MarcinWachowiak/analog-rf-phase-shifter-module/rf_phase_shifter_discrete_2_45GHz/qucs_sim_prj/plots/pha_l_ser_and_c_par_sweep.png

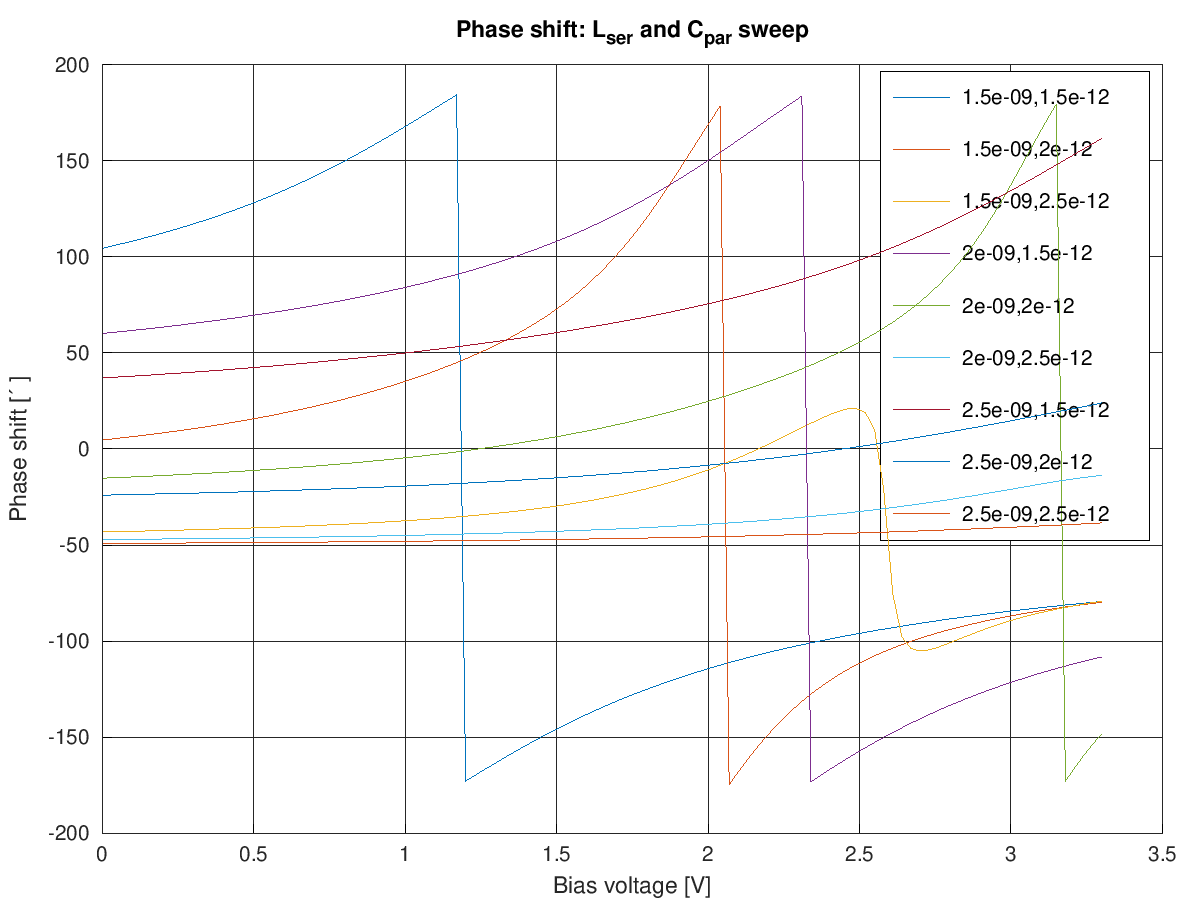
rf_phase_shifter_discrete_2_45GHz/qucs_sim_prj/plots/pha_l_ser_and_c_par_sweep.png
