MarcinWachowiak/analog-rf-phase-shifter-module/rf_phase_shifter_discrete_2_45GHz/qucs_sim_prj/plots/ripp_and_max_phase_shift_l_ser_sweep.png

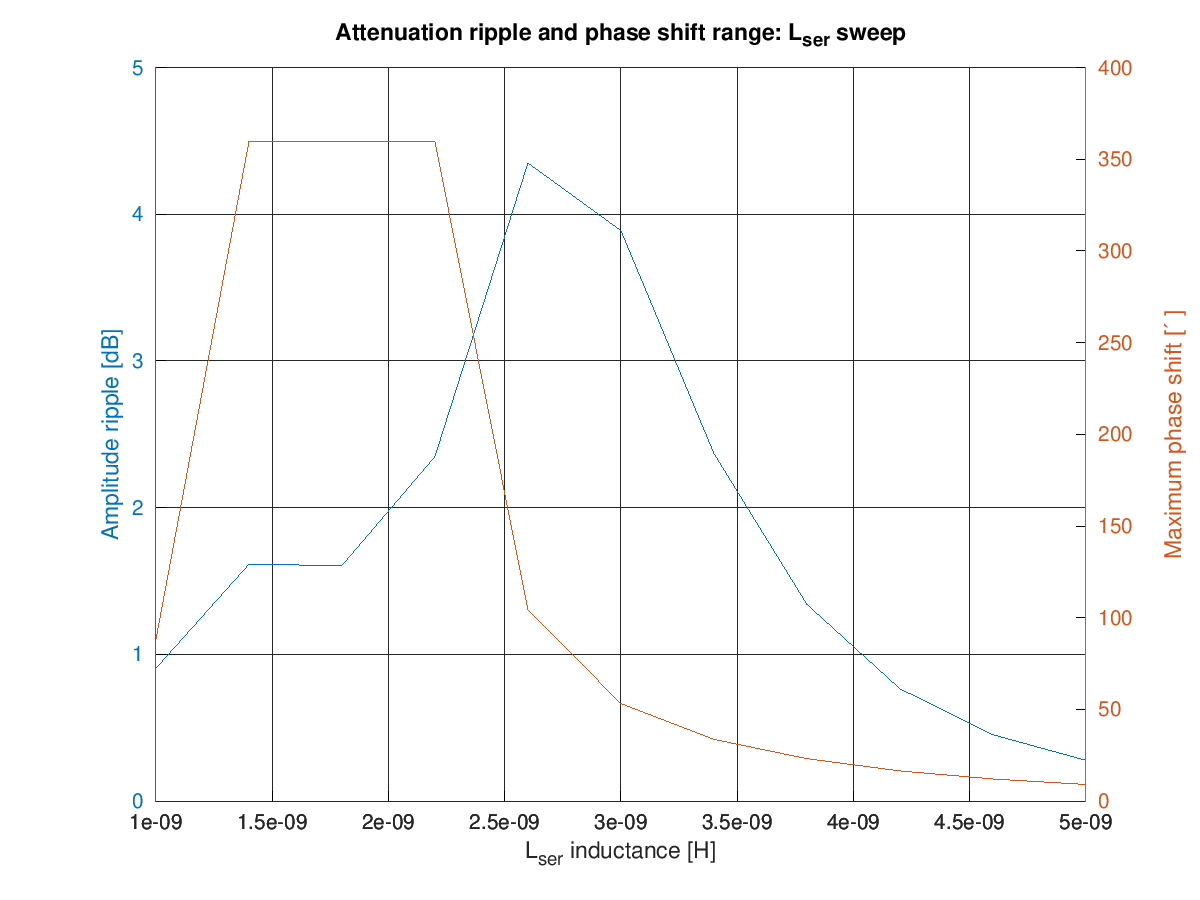
rf_phase_shifter_discrete_2_45GHz/qucs_sim_prj/plots/ripp_and_max_phase_shift_l_ser_sweep.png
