MarcinWachowiak/analog-rf-phase-shifter-module/rf_phase_shifter_distributed_2_45GHz/qucs_sim_prj/plots/att_tl24_imp_sweep.png

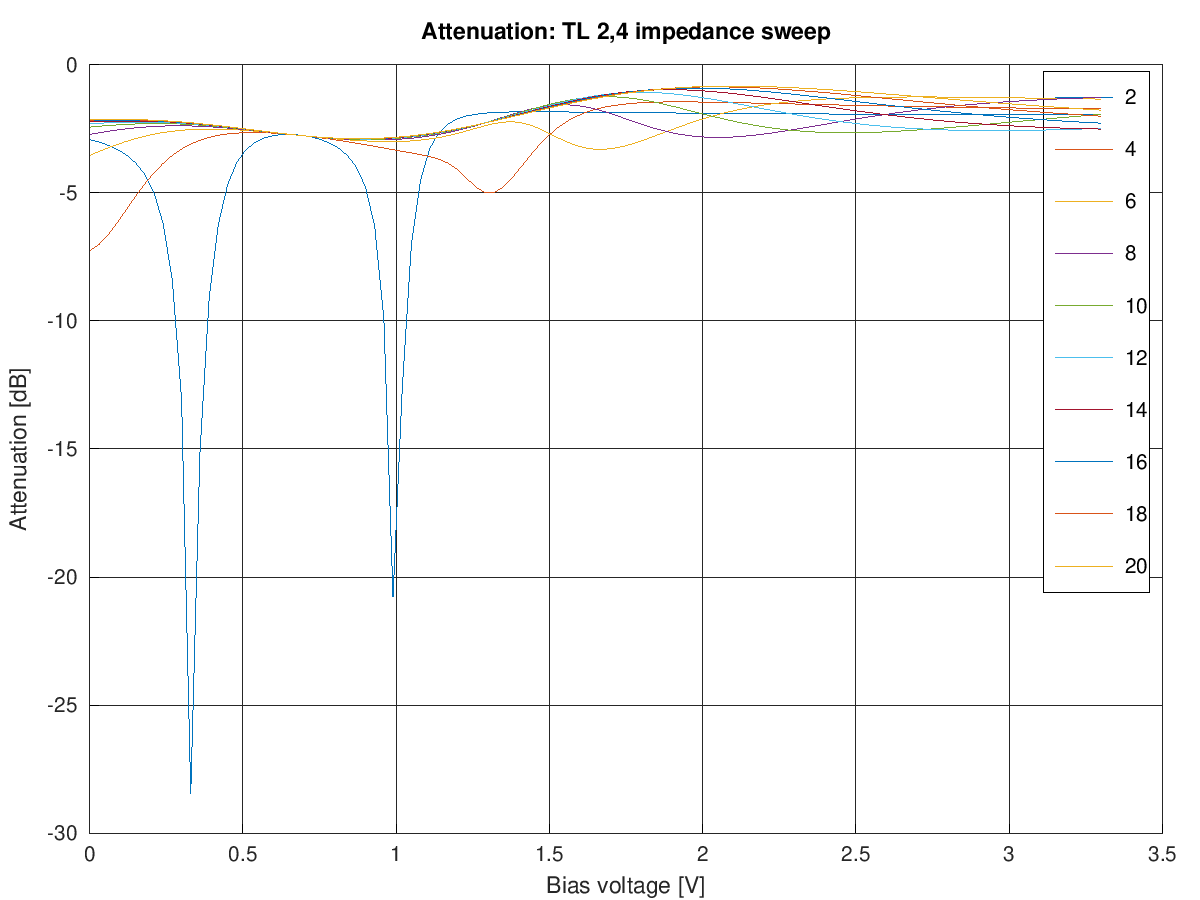
rf_phase_shifter_distributed_2_45GHz/qucs_sim_prj/plots/att_tl24_imp_sweep.png
