MarcinWachowiak/analog-rf-phase-shifter-module/rf_phase_shifter_distributed_2_45GHz/qucs_sim_prj/plots/ripp_and_max_phase_shift_tl24_len_sweep.png

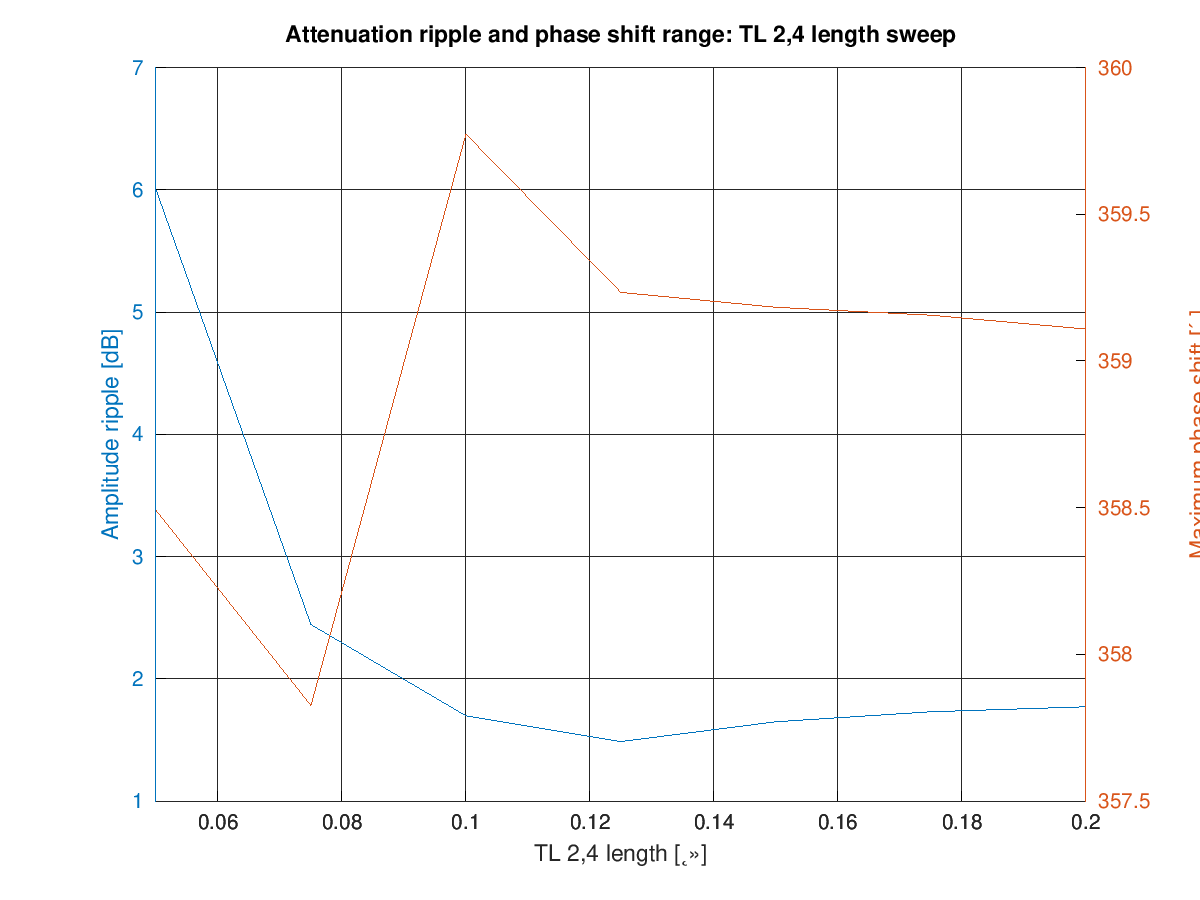
rf_phase_shifter_distributed_2_45GHz/qucs_sim_prj/plots/ripp_and_max_phase_shift_tl24_len_sweep.png
