MarcinWachowiak/analog-rf-phase-shifter-module/rf_phase_shifter_distributed_5_8GHz/qucs_sim_prj/plots/pha_tl13_imp_sweep.png

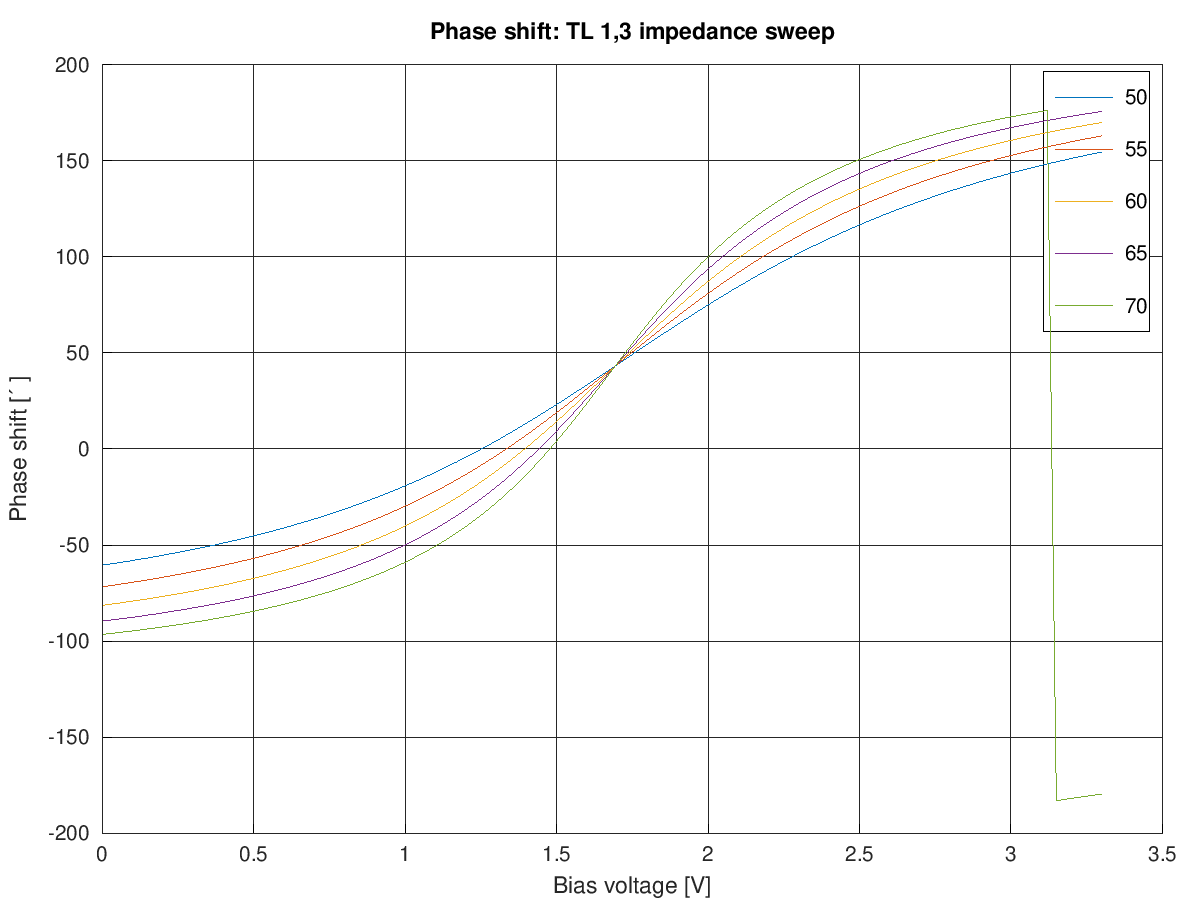
rf_phase_shifter_distributed_5_8GHz/qucs_sim_prj/plots/pha_tl13_imp_sweep.png
