MarcinWachowiak/analog-rf-phase-shifter-module/rf_phase_shifter_distributed_5_8GHz/qucs_sim_prj/plots/ripp_and_max_phase_shift_tl13_len_sweep.png

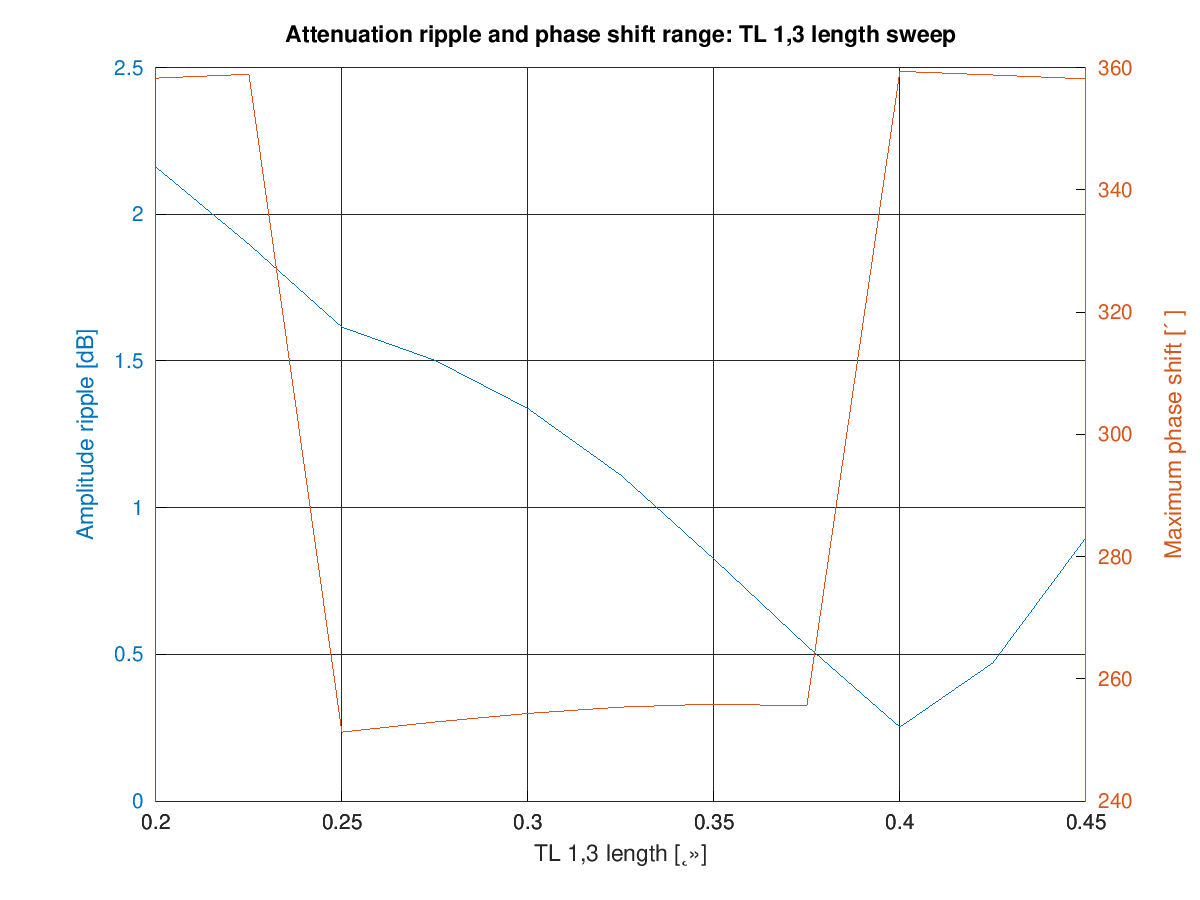
rf_phase_shifter_distributed_5_8GHz/qucs_sim_prj/plots/ripp_and_max_phase_shift_tl13_len_sweep.png
