MarcinWachowiak/analog-rf-phase-shifter-module/testbench/results/analog_rf_phase_shifter_discrete_2_45_GHz_tested_2400_2450_2500MHz_1.png

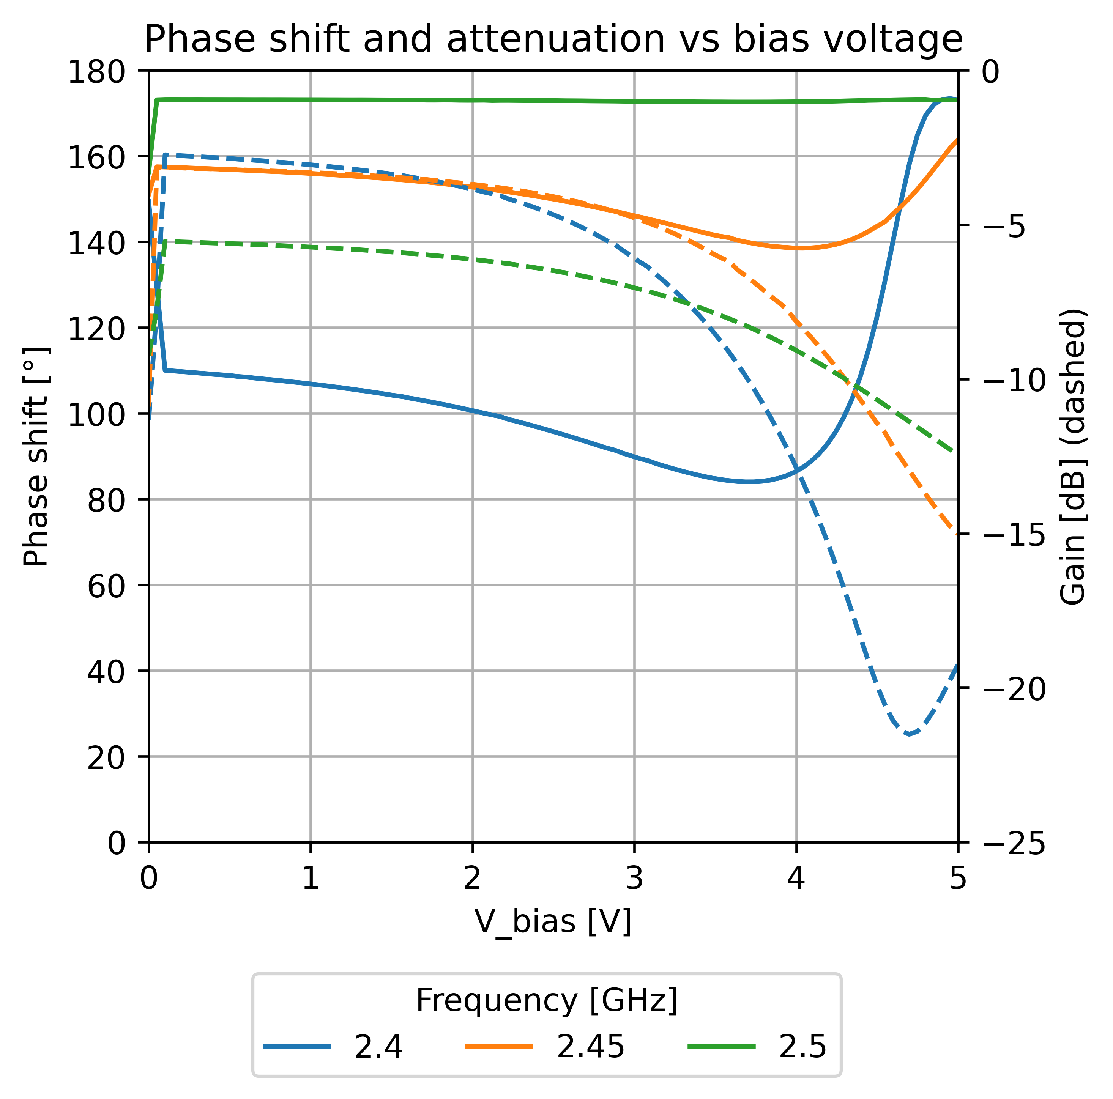
testbench/results/analog_rf_phase_shifter_discrete_2_45_GHz_tested_2400_2450_2500MHz_1.png
