MarcinWachowiak/analog-rf-phase-shifter-module/testbench/results/analog_rf_phase_shifter_distributed_2_45_GHz_tested_2400_2450_2500MHz.png

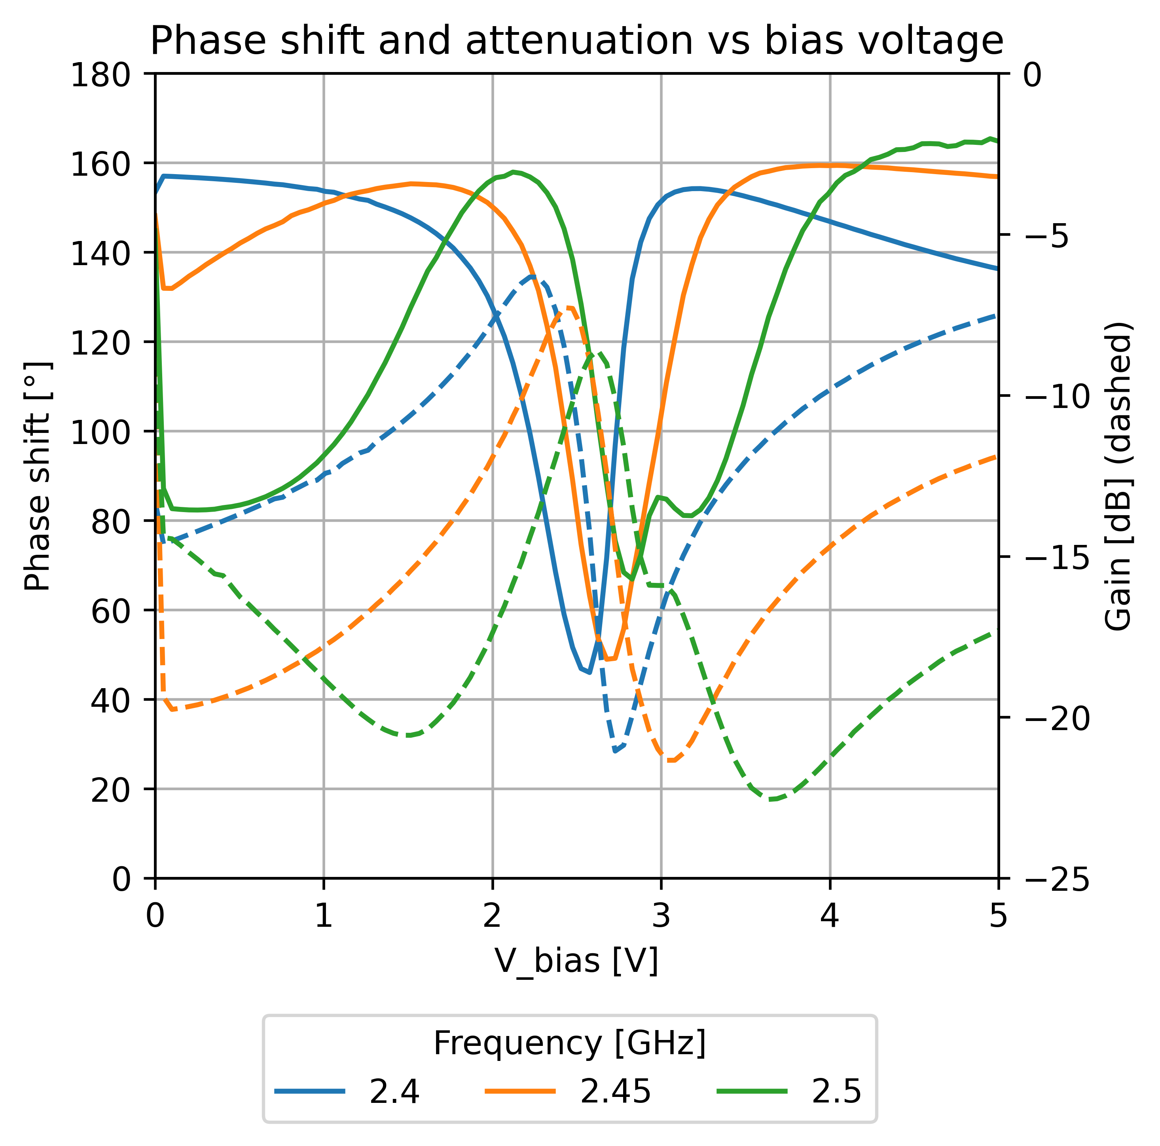
testbench/results/analog_rf_phase_shifter_distributed_2_45_GHz_tested_2400_2450_2500MHz.png
